EdwinJaraOFC/VentusSolarisAnalyzer/Documentacion/Talleres/Taller 04/T04Modelado3D.md

<p align="left">
  
  <h1 align="center">Taller 04: Modelado 3D</h1>
</p>

## 1. Descripción del Modelado 3D (Onshape)

### Características y componentes de Onshape

<p align="justify">
  
- **Modelado paramétrico:** Permite realizar cambios en el diseño de forma rápida y eficiente.<br>
- **Colaboración en tiempo real:** Los usuarios pueden trabajar en un mismo diseño de forma simultánea.<br>
- **Acceso basado en la nube:** Al estar basado en la nube, Onshape permite a los usuarios acceder a sus diseños desde cualquier dispositivo con conexión a internet.<br>
- **Versionado automático:** Onshape guarda automáticamente el historial de versiones de los diseños
</p>

### Importancia del Onshape como herramienta para la creación del modelado 3D

<p align="justify">
Onshape es una herramienta importante para el modelado 3D debido a su accesibilidad, capacidad de colaboración, modelado paramétrico y herramientas integradas para simulaciones y pruebas de rendimiento. Estas características hacen de Onshape una plataforma integral y poderosa para el diseño y la ingeniería colaborativa en 3D.
</p>

## 2. Materiales
- Laptop e implementos
- Software CAD (Onshape)
- Impresora 3D

## 3. Desarrollo de ejercicios
### Ejercicio 1: Representación de un vaso a partir de un círculo

<p align="justify">
Para realizar la representación de un vaso 3D, nos ubicamos en la vista “Top” para añadir un círculo con dimensiones de 60mm, luego nos encargamos de que el círculo se encuentre centrado con la opción “Concentric”.
</p>

<div align="center"; style="display: flex; justify-content: space-between;">
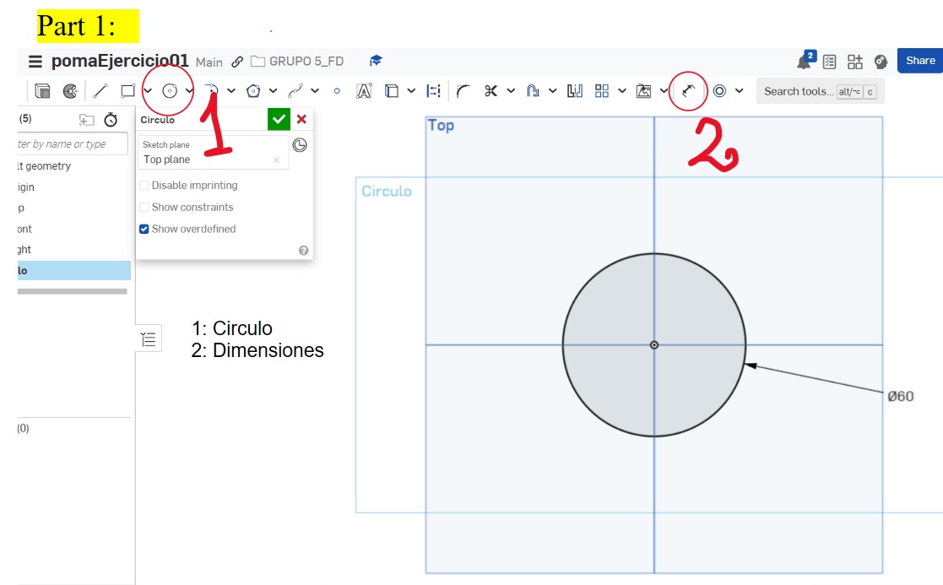
[picture p34: Documentacion/Talleres/Taller 04/Imagenes/T04Imagen01.jpg]
  
</div>

<p align="justify">
Luego realizamos las accion “Extrude” para pasar de un modelo 2D a un modelo 3D con ciertas medidas.
</p>

<div align="center"; style="display: flex; justify-content: space-between;">
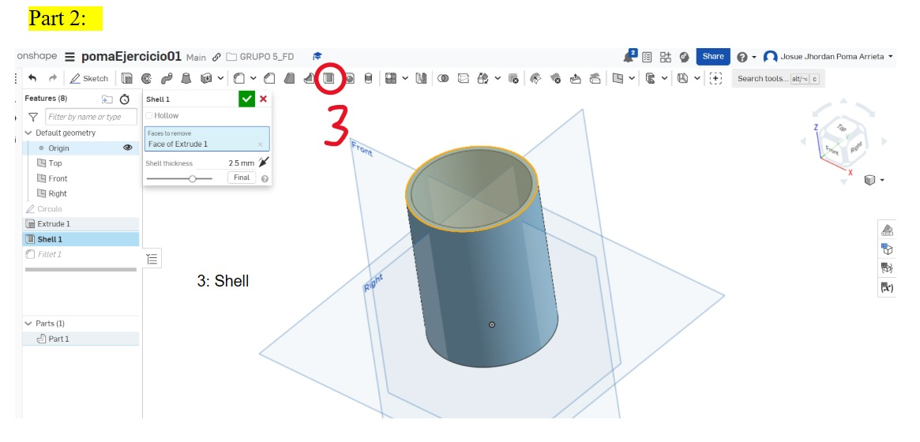
[picture p35: Documentacion/Talleres/Taller 04/Imagenes/T04Imagen02.jpg]
  
</div>

<p align="justify">
Después pasamos a quitarle la parte superior del vaso para que se parezca cada vez más un vaso, con la opción de “Shell”.
</p>

<div align="center"; style="display: flex; justify-content: space-between;">
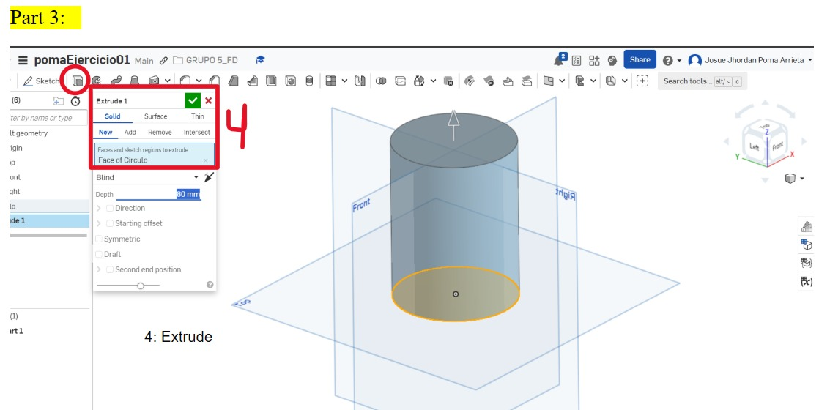
[picture p36: Documentacion/Talleres/Taller 04/Imagenes/T04Imagen03.jpg]
  
</div>

<p align="justify">
Le dimos bordes con la opción “Fillet”, quedando nuestro vaso de la siguiente manera:
</p>

<div align="center"; style="display: flex; justify-content: space-between;">
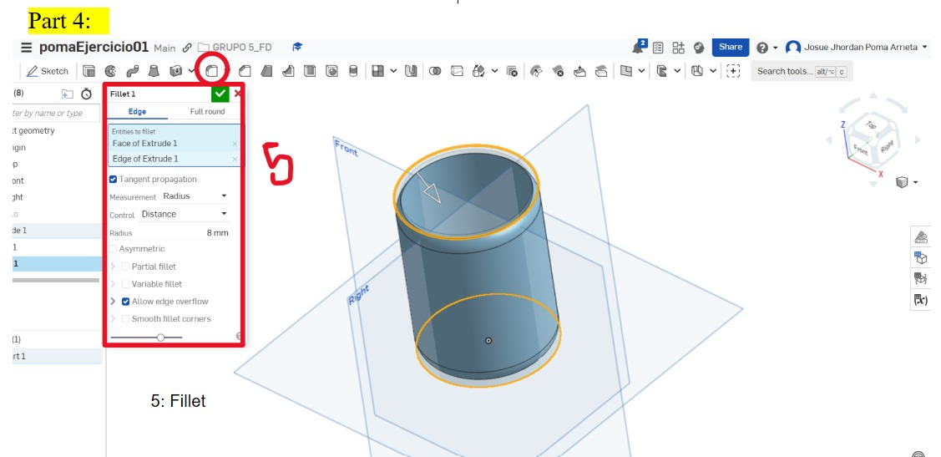
[picture p37: Documentacion/Talleres/Taller 04/Imagenes/T04Imagen04.jpg]
  
</div>

<p align="justify">
Después escogimos que color queríamos para el vaso y lo seleccionamos.
</p>

<div align="center"; style="display: flex; justify-content: space-between;">
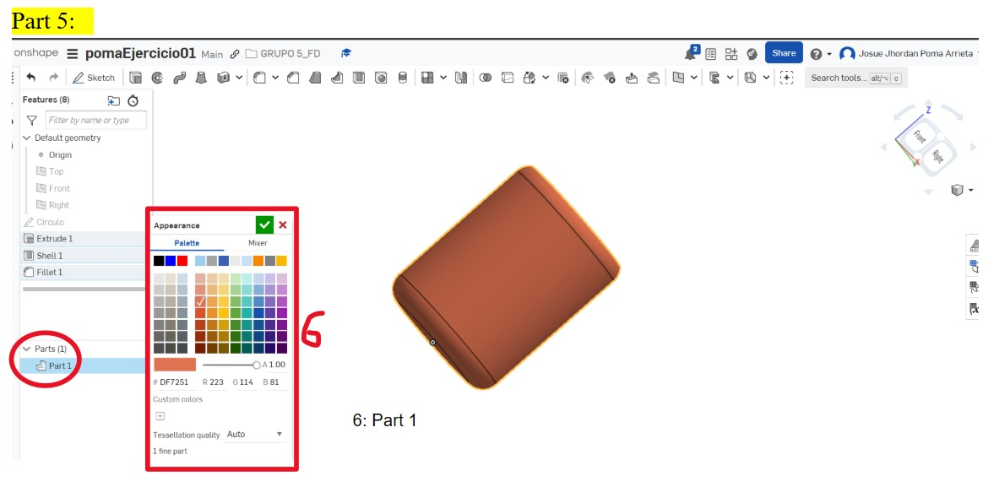
[picture p38: Documentacion/Talleres/Taller 04/Imagenes/T04Imagen05.jpg]
  
</div>

<p align="justify">
Finalmente quedando nuestro diseño del vaso de la siguiente manera:
</p>

<div align="center"; style="display: flex; justify-content: space-between;">
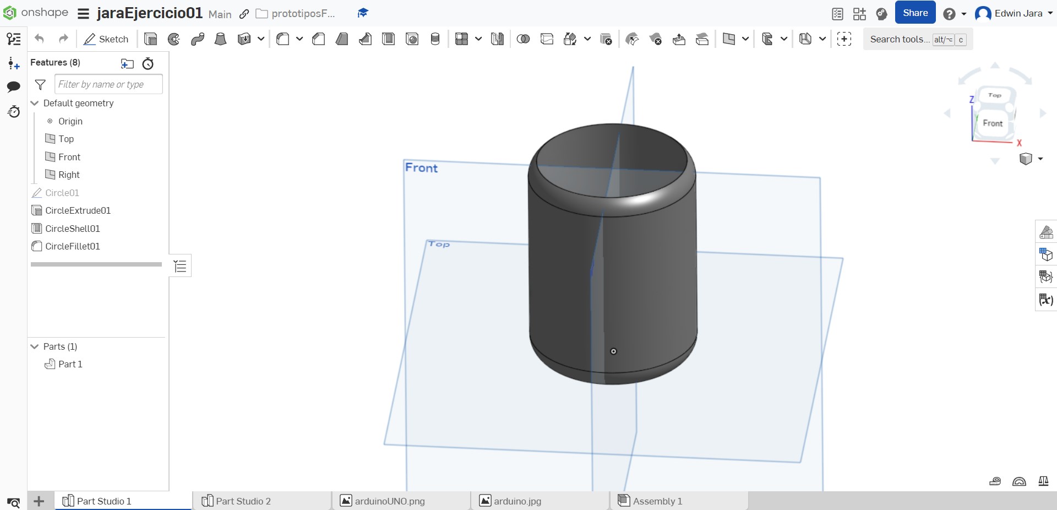
[picture p39: Documentacion/Talleres/Taller 04/Imagenes/T04Imagen06.jpg]
  
</div>

### Ejercicio 2: Representación de un vaso a partir de líneas

Para realizar la representación de un vaso 3D a partir de líneas, comenzamos en la vista "front" y creamos un sketch donde agregamos líneas para esbozar la mitad del vaso en 2D. Utilizando funciones aprendidas en el ejercicio 1, transformamos este diseño bidimensional en uno tridimensional. Las herramientas empleadas permitieron extruir y dar forma al vaso 2D, generando así la representación final en 3D, como se muestra en la segunda imagen.

<div align="center"; style="display: flex; justify-content: space-between;">
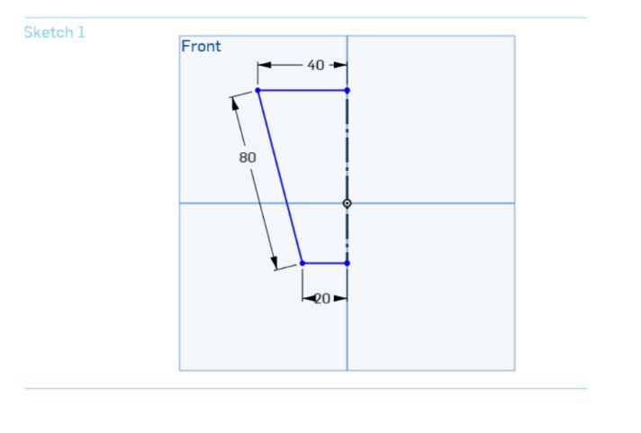
[picture p40: Documentacion/Talleres/Taller 04/Imagenes/T04Imagen07.jpg]
  
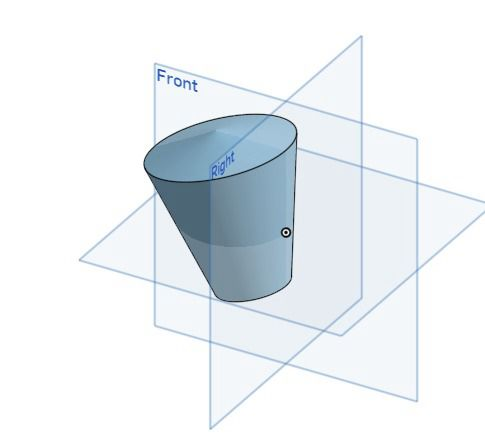
[picture p41: Documentacion/Talleres/Taller 04/Imagenes/T04Imagen08.jpg]
  
</div>

### Ejercicio 3: Representación de una taza a partir del ejercicio 1

<p align="justify">
Para modelar la taza tuvimos que usar el molde ya hecho de un vaso en el ejercicio 1, partimos ese molde y lo transformamos en una taza funcional y estéticamente diferente al añadirle una asa. Comenzamos dibujando la asa con la herramienta "3 point arc" en un nuevo sketch, ajustándola cuidadosamente para que se integrara bien con la forma existente del vaso. Luego, utilizando las herramientas de modelado en 3D, dimos volumen y forma ergonómica a la asa, haciendo ajustes hasta lograr un diseño atractivo. Finalmente, refinamos la transición entre la asa y el cuerpo del vaso para obtener una apariencia suave y cohesiva.
</p>

<div align="center"; style="display: flex; justify-content: space-between;">
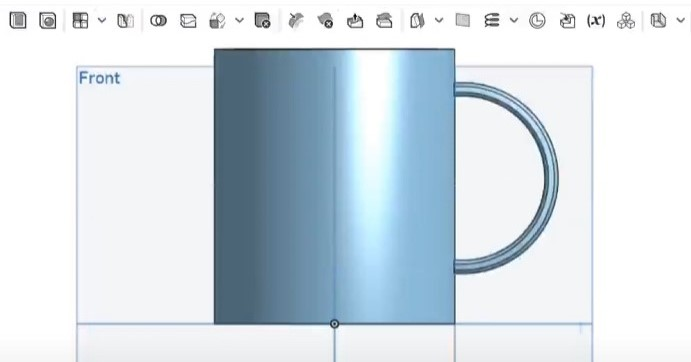
[picture p42: Documentacion/Talleres/Taller 04/Imagenes/T04Imagen22.jpg]
  
</div>

### Ejercicio 4: Representación de un case para Arduino UNO

<p align="justify">
Para realizar la representación del case Arduino UNO, empezamos insertando una imagen en un sketch en “top” y redimensionando un poco para posteriormente empezar a hacer el case.
</p>

<div align="center"; style="display: flex; justify-content: space-between;">
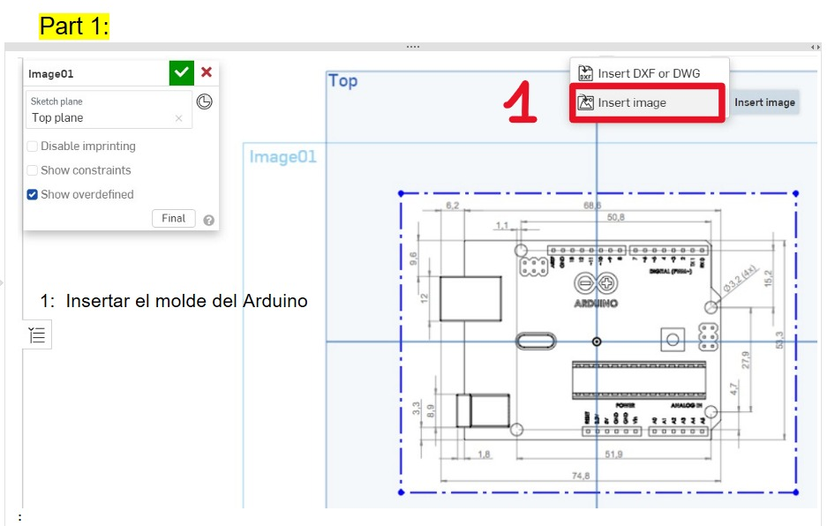
[picture p43: Documentacion/Talleres/Taller 04/Imagenes/T04Imagen13.jpg]
  
</div>

<p align="justify">
Luego de insertar la imagen procedemos a crear un sketch en “top” e insertar líneas tomando la forma del case, luego procedemos a insertar las dimensiones correspondientes.
</p>

<div align="center"; style="display: flex; justify-content: space-between;">
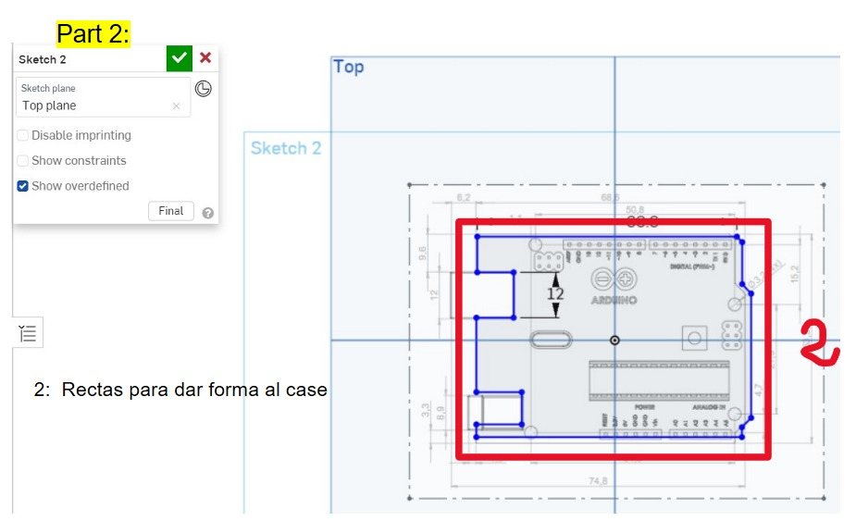
[picture p44: Documentacion/Talleres/Taller 04/Imagenes/T04Imagen14.jpg]
  
</div>

<p align="justify">
Luego usamos la función “extrude” con las líneas hechas anteriormente para darle la forma 3D a nuestro trabajo.
</p>

<div align="center"; style="display: flex; justify-content: space-between;">
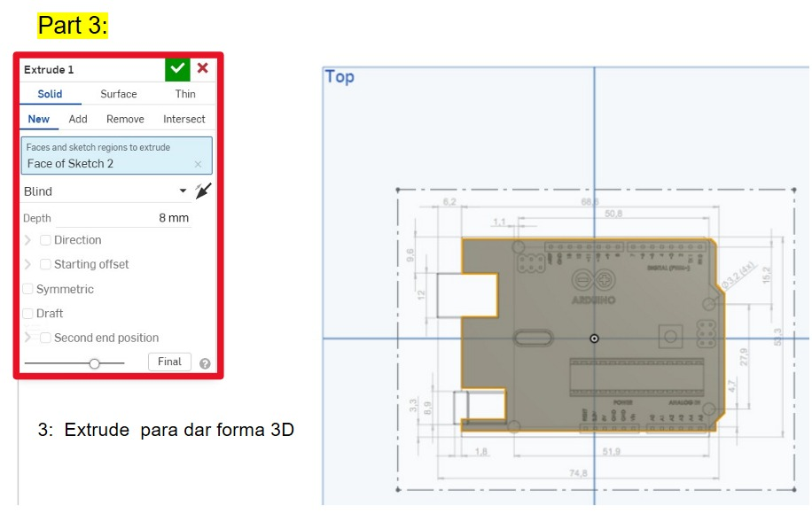
[picture p45: Documentacion/Talleres/Taller 04/Imagenes/T04Imagen15.jpg]
  
</div>

<p align="justify">
Luego decidimos quitarle la tapa para que se asemeje al case del Arduino UNO, junto con asignarle un grosor que fue de 1mm.
</p>

<div align="center"; style="display: flex; justify-content: space-between;">
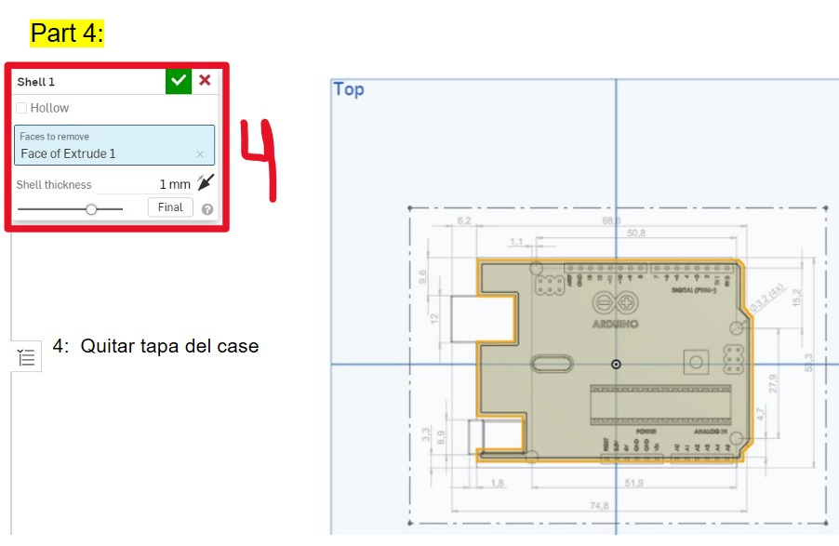
[picture p46: Documentacion/Talleres/Taller 04/Imagenes/T04Imagen16.jpg]
  
</div>

<p align="justify">
Paso extra: Tuvimos que recortar las partes que hacían que el case no entre correctamente luego de darnos cuenta en la impresión 3D, lo hicimos creando un sketch nuevo y dando la forma del rectángulo.
</p>

<div align="center"; style="display: flex; justify-content: space-between;">
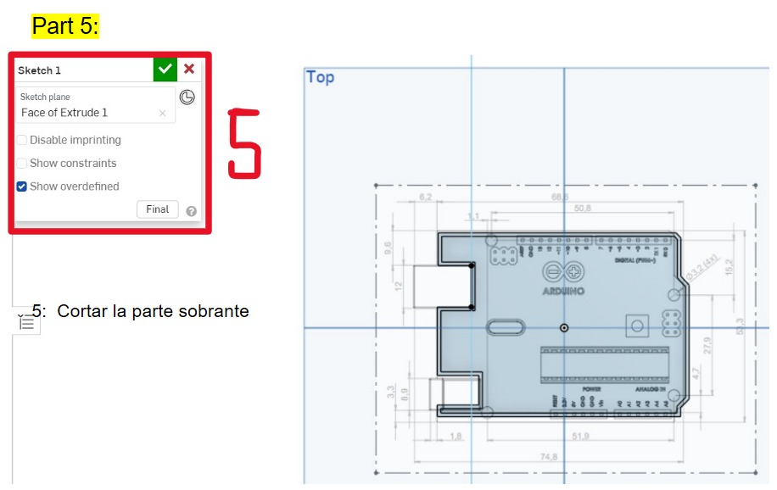
[picture p47: Documentacion/Talleres/Taller 04/Imagenes/T04Imagen17.jpg]
  
</div>

<p align="justify">
Paso extra: Usamos la función "extrude" pero con la diferencia de que esta vez la usamos parar borrar la parte que no necesitabamos del case, usando anteriormente los rectángulos, luego ajustamos y damos en enter para completar la eliminación de ese espacio.
</p>

<div align="center"; style="display: flex; justify-content: space-between;">
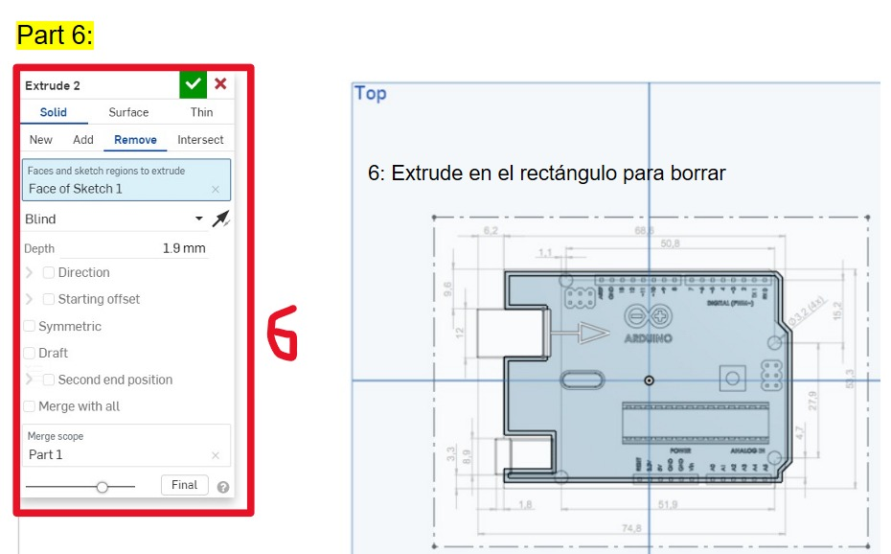
[picture p48: Documentacion/Talleres/Taller 04/Imagenes/T04Imagen18.jpg]
  
</div>

<p align="justify">
Y al final de todos estos pasos el modelado del case Arduino UNO nos quedó de la siguiente manera:
</p>

<div align="center"; style="display: flex; justify-content: space-between;">
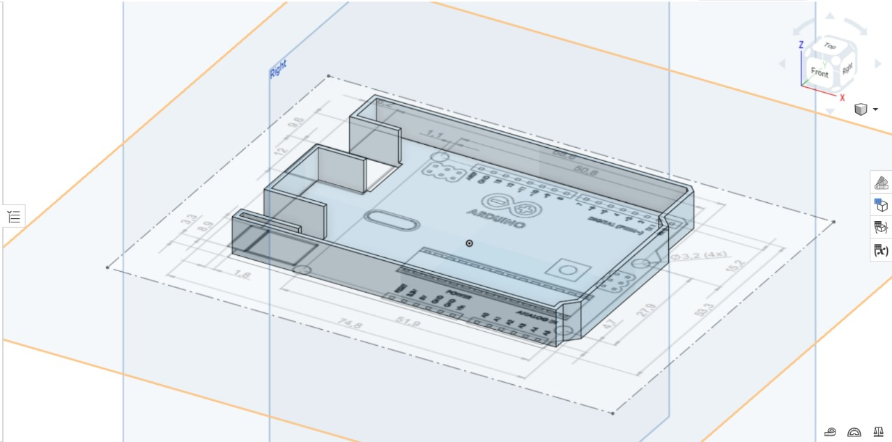
[picture p49: Documentacion/Talleres/Taller 04/Imagenes/T04Imagen19.jpg]
  
</div>

<br>
<p align="justify">
Al momento de imprimir nuestro modelado 3D no tomamos en cuenta que el case debía tener un grosor mínimo de 5mm, nosotros lo hicimos con un grosor de 1mm, por lo que nuestro case salió delgado, y tuvimos otro pequeño error de no considerar los espacios de las entradas del Arduino. Anotamos estos errores para no volverlos a cometer en un futuro.
</p>

<div align="center"; style="display: flex; justify-content: space-between;">
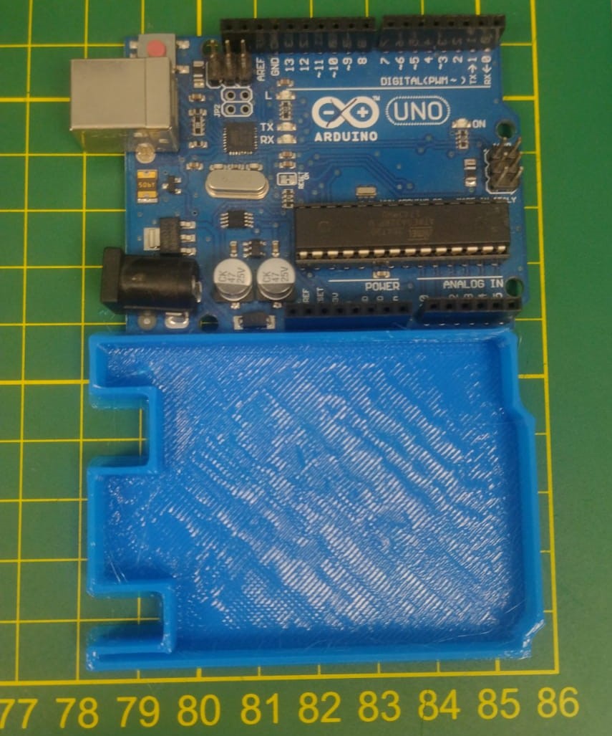
[picture p50: Documentacion/Talleres/Taller 04/Imagenes/T04Imagen20.jpg]
  
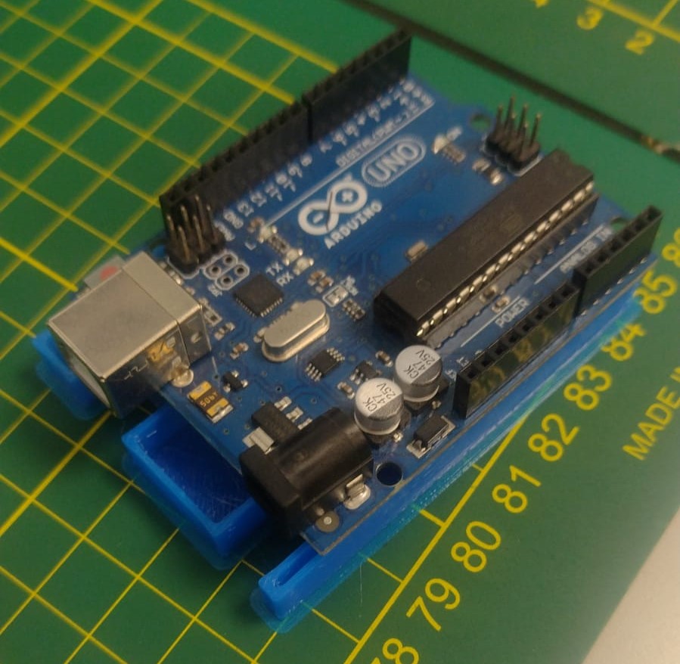
[picture p51: Documentacion/Talleres/Taller 04/Imagenes/T04Imagen21.jpg]
  
</div>

## 4. Evidencias del desarrollo de ejercicios

<div align="center"; style="display: flex; justify-content: space-between;">
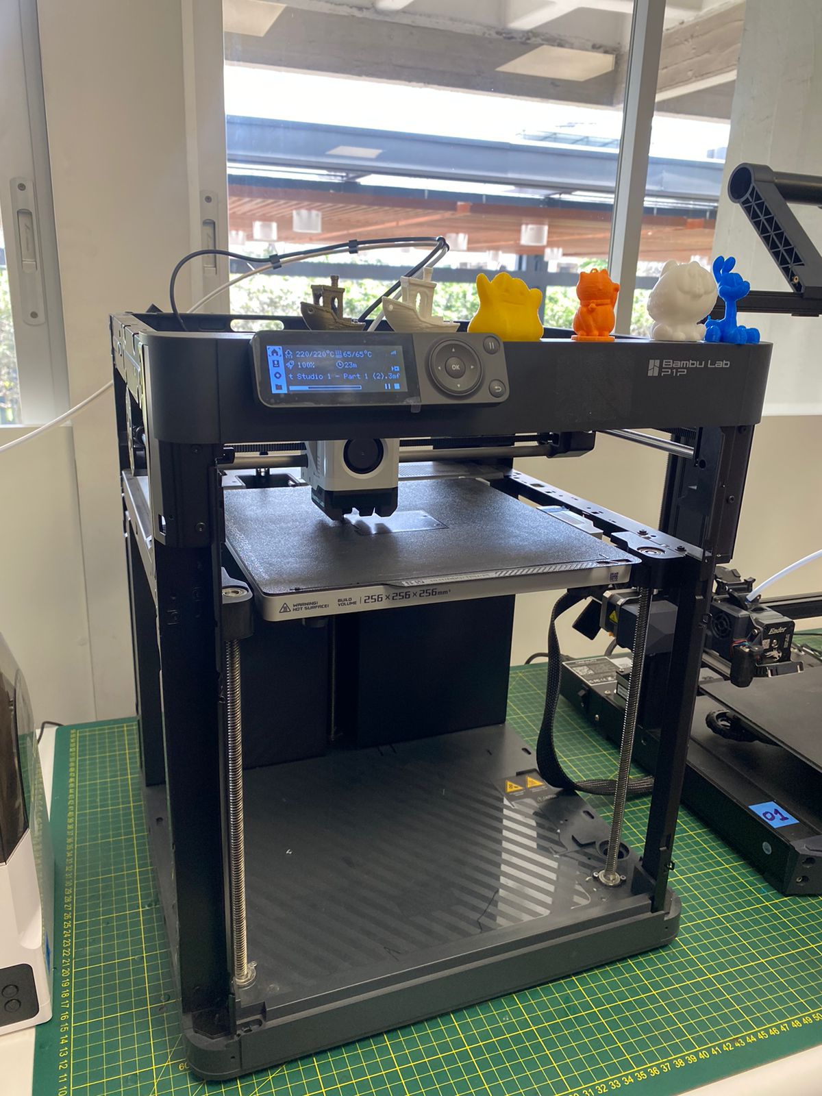
[picture p52: Documentacion/Talleres/Taller 04/Imagenes/T04Imagen09.jpg]
  
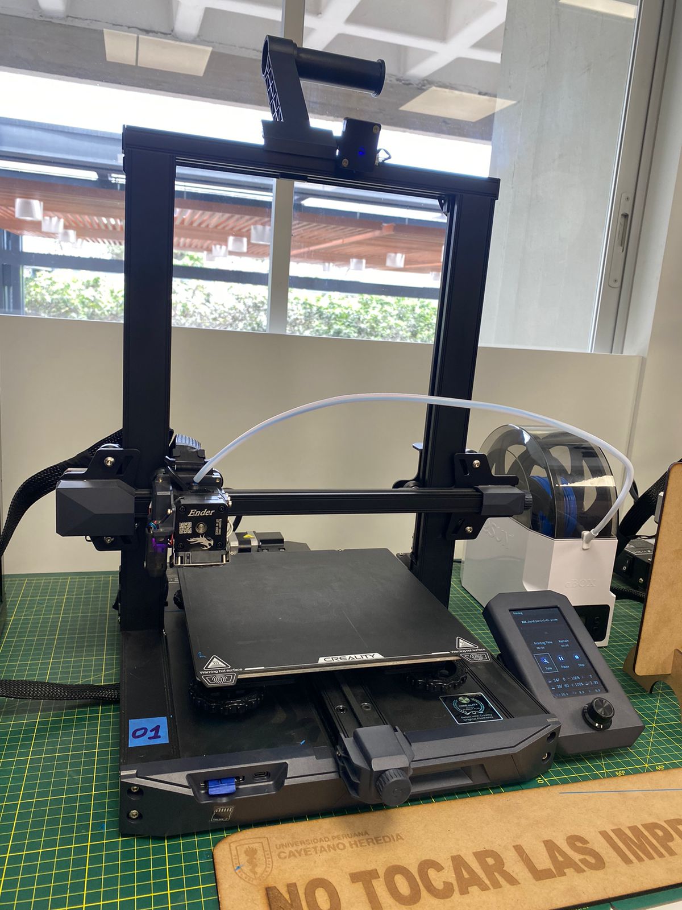
[picture p53: Documentacion/Talleres/Taller 04/Imagenes/T04Imagen10.jpg]
  
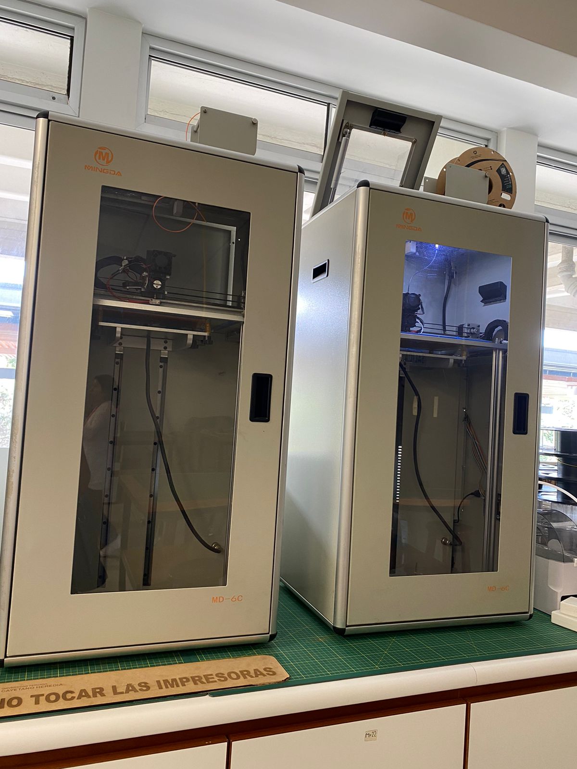
[picture p54: Documentacion/Talleres/Taller 04/Imagenes/T04Imagen11.jpg]
  
</div> 
</div>
<div align="center"; style="display: flex; justify-content: space-between;">
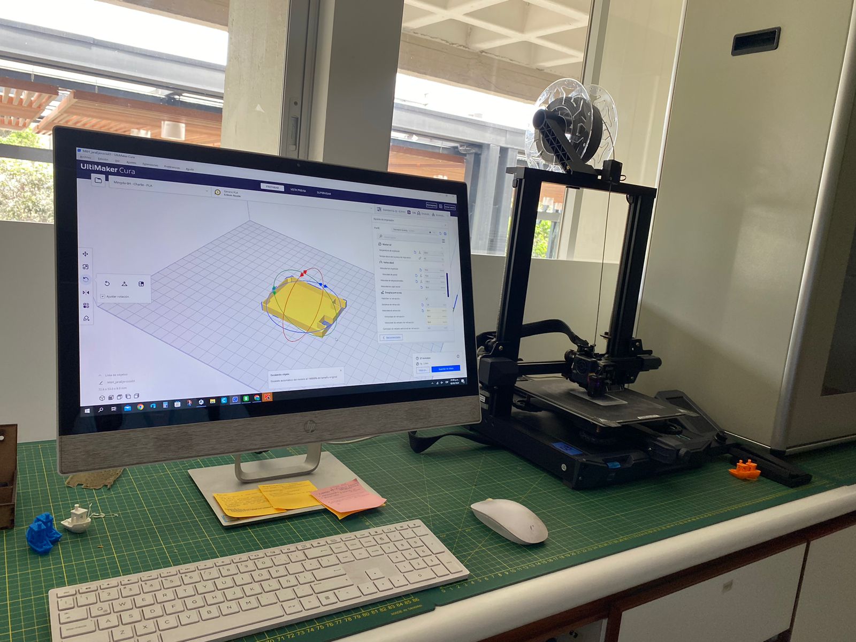
[picture p55: Documentacion/Talleres/Taller 04/Imagenes/T04Imagen12.jpg]
  
</div>

## 5. Conclusión

<p align="justify">
Durante la sesión de clase en la que modelamos una vaso ,  taza en la aplicación de Onshape y posteriormente creamos un estuche para un Arduino, adquirimos conocimientos prácticos sobre el modelado en 3D y la aplicación de Onshape. Esta experiencia nos permitió aplicar las habilidades aprendidas en un entorno práctico y nos preparó para el proceso de impresión 3D. En resumen, esta actividad fue fundamental para el desarrollo de nuestras habilidades en el campo del diseño y la fabricación digital.
</p>
