EdwinJaraOFC/VentusSolarisAnalyzer/Documentacion/Presentaciones/Proyectos de Ingenieria/Hito01.pdf

# INTEGRANTES:

# Florian Párraga, Josué Abel Jara Bocanegra, Edwin Junior Pérez Amado, Romina Alisson Pérez Damián, Cindy Mayomi

Vásquez Nuñez America Mailyn | GRUPO N°6

# "Ventus Solaris"

# Deseos:

"Sistema portátil de baja potencia a base de
sensores | que | puedan | monitorear | las características de la radiación solar y la

velocidad del viento, con el objetivo de transmitir datos desde los sensores y dispositivos IoT a una

plataforma en la nube de gestión centralizada".

Problematica: Falta de acceso a la electricidad

en el colegio San José Obrera 15357, específicamente en el km 41 carretera a Chulucanas.

Autoridades locales interesadas en mejorar el acceso a la energía en la zona rural, con el objetivo de garantizar que las actividades educativas del colegio San José Obrero no se

vean interrumpidas por cortes prolongados de electricidad.

## Solución:

## Lugar de estudio:

I.E. San Jose Obrero - Morropón, Chulucanas - Piura

## REQUERIMIENTOS PARA EL USUARIO:

Necesidades: Acceso Continuo a la Electricidad Costo Accesible Fiabilidad para la Educación Facilidad de Mantenimiento

Deseos: Capacitación del personal Mejora de la Infraestructura Educativa

Impacto en la Comunidad Durabilidad a Largo Plazo

# Requerimientos del Sistema:

# Necesidades:

Fácil Configuración y Operación Medición | Precisa | de | Variables Climáticas Autonomía Energética Bajo Costo de Producción Portabilidad
Optimización del Consumo de Energía Capacidad de Almacenamiento

Local Resiliencia Climática Conectividad para Transmisión de Datos

## Usuarios (stakeholders):

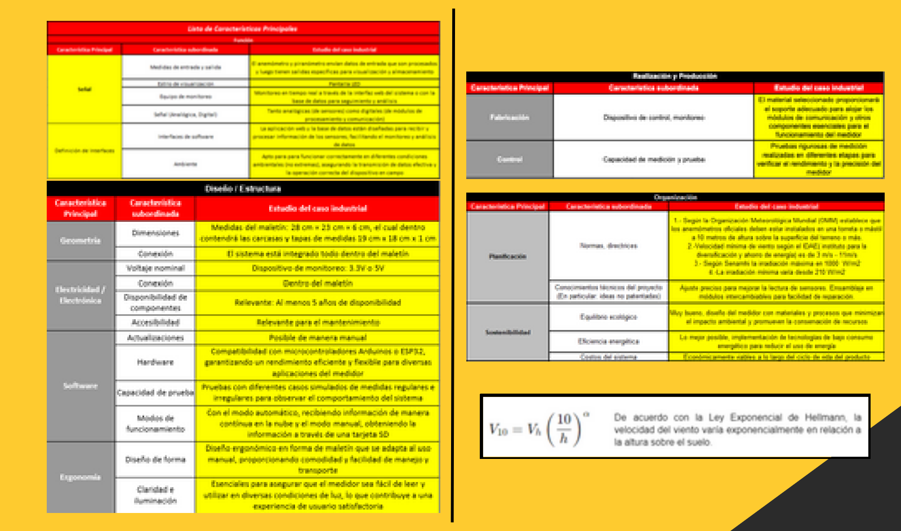
[picture p56: page 3]
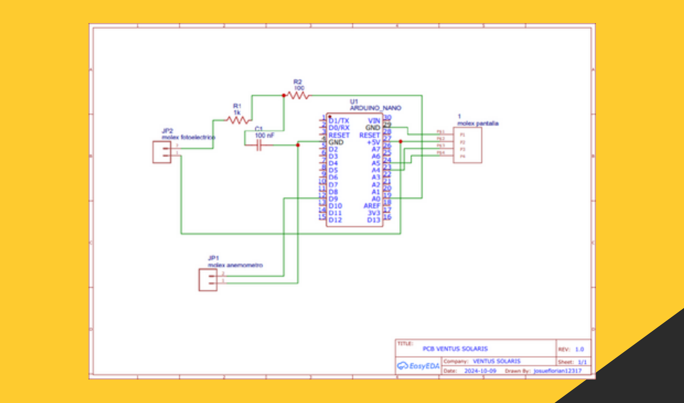
[picture p57: page 4]

# PCB DEL CIRCUITO ELECTRÓNICO

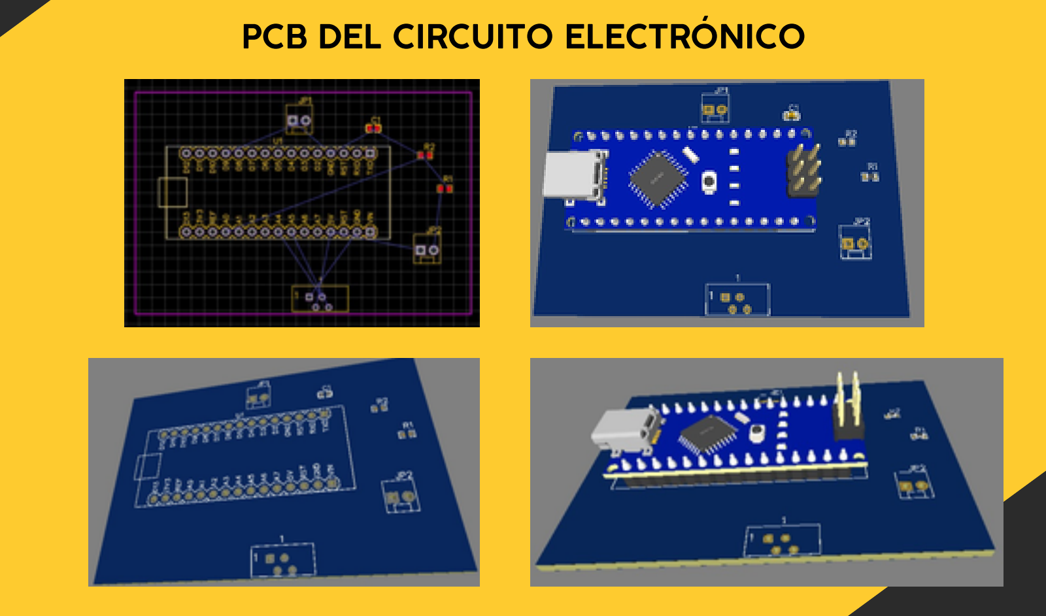
[picture p58: page 5]

# COMPONENTES PRINCIPALES

PCB DEL CIRCUITO ELECTRÓNICO.

Objetivo del Proyecto: Desarrollar un sistema portátil de baja potencia que monitoriza: Radiación solar (Sensor SUF268J001). Velocidad del viento (Anemómetro casero con motor RF-500TB-14415).

Arduino Nano
(Microcontrolador)

Sensor de Radiación Solar (SUF268J001)

Anemómetro Casero

Pantalla I2C

Conectores Molex

Facilitan | conexiones modulares de sensores y pantalla, asegurando fácil mantenimiento

Muestra datos en tiempo real (radiación solar y velocidad del viento). Comunicación vía pines A4

(SDA) y A5 (SCL).

Calcula la velocidad del viento en función de las revoluciones del motor. Envía la señal al pin ADC (A1) del Arduino.

Mide la intensidad de la
radiación solar. Envía datos al pin ADC

(A0) del Arduino Nano.

Controla los sensores y la pantalla I2C. Alimenta los componentes a

través de sus pines de 5V.

# VENTAJAS:

Modularidad: Uso de conectores Molex para rápida desconexión y ajuste de componentes. Eficiencia Energética: Optimizado

para bajo consumo con alimentación de batería portátil. Portabilidad: Diseño compacto para

fácil instalación en campo.

Conclusión: El sistema portátil para medir la velocidad del viento y la radiación solar está diseñado

para proporcionar datos precisos y en tiempo real, facilitando la evaluación de proyectos de energía renovable. El uso de conectores Molex y un diseño optimizado

garantiza la modularidad, eficiencia y facilidad de uso del sistema en campo.

# COMPONENTES

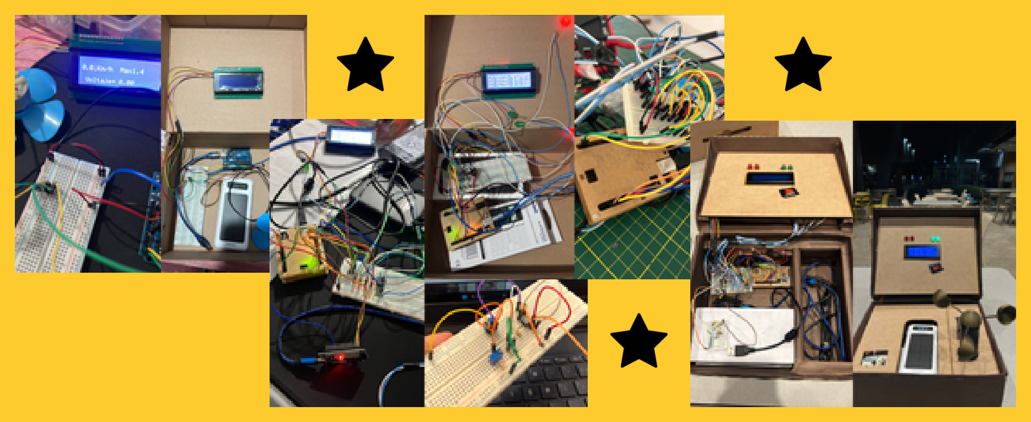
[picture p59: figure]

Álvarez, C. (2006, September). Energía eólica (IDAE, Ed.) [Review of Energía eólica]. Instituto Para La Diversificación Y Ahorro de La Energía; | Instituto | para | la | Diversificación | y | Ahorro | de | la | Energía. http://www.esengrupo.com/uploads/descargas/archivo/Manual%20de%20Energ%C3%ADa%20E%C3%B3lica%20IDAE.pdf

Fap Wilar, M., Molina, G., Fap, C., Cruzado, R., Senamhi, D., & Quijandría Salmón, J. (n.d.). SERVICIO NACIONAL DE METEOROLOGÍA E HIDROLOGÍA DIRECCIÓN GENERAL DE INVESTIGACIÓN Y ASUNTOS AMBIENTALES MINISTERIO DE

ENERGÍA Y MINAS DIRECCIÓN EJECUTIVA DE PROYECTOS REPÚBLICA DEL PERÚ ATLAS DE ENERGÍA SOLAR DEL PERÚ. https://www.senamhi.gob.pe/pdf/Atlas%20_de_Radiacion_Solar.pdf

Ruíz de Alegría, A. (2020). Estudio complementario de impacto de la radiación UV en paneles solares (datos UV de un año) y otros componentes expuestos en condiciones del altiplano boliviano (Dirección General de Energías AlternativaS, Ed.) [Review of Estudio complementario de impacto de la radiación UV en paneles solares (datos UV de un año) y otros componentes expuestos en condiciones del altiplano boliviano]. Electricidad Y Energías Alternativas; Programa de Energías Renovables (PEERR). https://energypedia.info/images/3/31/APRBADO_INFORME_estudio_UV.pdf

Uribe, I. M. (2018). Valoración del viento como fuente de energía eólica en el estado de Guerrero. Ingeniería, 22(3), 30-46. https://www.redalyc.org/journal/467/46759491003/46759491003.pdf

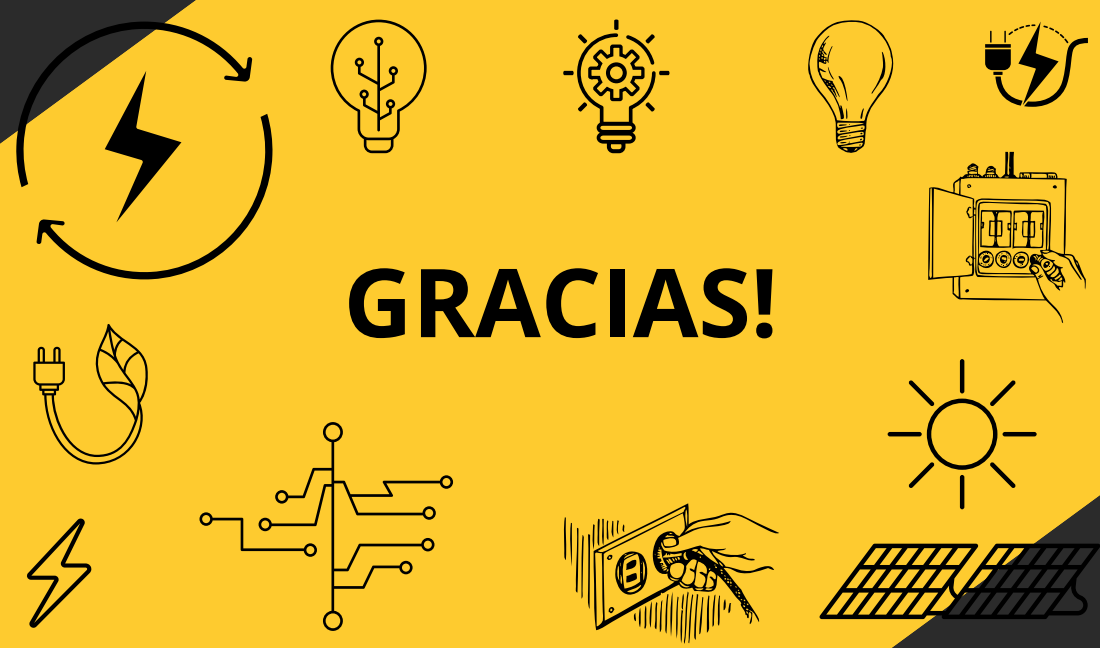
[picture p60: page 9]
GRACIAS!
