EdwinJaraOFC/VentusSolarisAnalyzer/Prototipo/README.md

<p align="left">
  
  <h1 align="center">Desarrollo de Prototipo</h1>
</p>

<p align="justify">La carpeta Prototipo contiene todos los recursos necesarios para la creación, implementación y pruebas del prototipo del proyecto VentusSolaris Analyzer. Aquí se encuentra la documentación y los archivos que respaldan el desarrollo técnico del hardware y software, así como los resultados de las pruebas realizadas.</p>

## Estructura de la Carpeta

### 1. Diseño

- Esquemas y planos del prototipo.
- Documentos relacionados con el diseño conceptual y técnico.
- Diagramas y modelos 3D, si están disponibles.

### 2. Hardware

- Especificaciones de los componentes electrónicos y mecánicos utilizados.
- Esquemas de conexión y diagramas de circuitos.
- Manuales de instalación y configuración del hardware.

### 3. Software

- Código fuente del proyecto.
- Scripts y programas necesarios para la operación del prototipo.
- Documentación sobre las dependencias y configuraciones del software.

### 4. Tests

- Resultados de las pruebas realizadas al prototipo.
- Métodos de validación para hardware y software.
- Registros de errores y mejoras propuestas.

## Propósito

<p align="justify">La carpeta Prototipo está diseñada para ofrecer una visión integral del proceso de desarrollo técnico, desde el diseño inicial hasta las pruebas finales. Su contenido está orientado a:</p>

1. Facilitar la replicación del prototipo por otros equipos interesados en el proyecto.
2. Documentar los avances y resultados obtenidos durante las etapas de desarrollo.
3. Optimizar el diseño a través de pruebas continuas y retroalimentación.

## Uso

1. Explora la carpeta Diseño para comprender la planificación inicial del prototipo.
2. Revisa el apartado Hardware para ensamblar y configurar los componentes físicos.
3. Consulta la sección Software para implementar y ejecutar el código del proyecto.
4. Verifica la carpeta Tests para analizar los resultados y evaluar el desempeño del sistema.

## Contribuciones

<p align="justify">Si deseas colaborar en la mejora del prototipo, consulta los documentos dentro de las carpetas Diseño y Tests para identificar áreas de mejora y proponer cambios. Asegúrate de seguir las guías de contribución detalladas en el README general.</p>
