EdwinJaraOFC/VentusSolarisAnalyzer/Prototipo/Diseño/README.md

<p align="left">
  
  <h1 align="center">Diseño del Prototipo</h1>
</p>

<p align="justify">Esta carpeta contiene los recursos y documentos relacionados con el diseño estructural y conceptual del proyecto VentusSolaris Analyzer. Incluye desde los modelos iniciales hasta el diseño final del prototipo.</p>

## Contenido

- <strong>D01ModeladoBase:</strong> Documentación del modelado inicial, incluyendo conceptos preliminares y bocetos.

- <strong>D02PlanosBase:</strong> Planos técnicos que detallan las dimensiones y estructuras del prototipo.

- <strong>D03DiseñoFinal:</strong> Representación del diseño final aprobado para la fabricación y ensamblaje.

## Uso

- Revisa el modelado base para comprender las ideas iniciales del diseño.
- Consulta los planos base para obtener especificaciones técnicas del prototipo.
- Explora el diseño final como referencia para la implementación y mejoras futuras.
