EdwinJaraOFC/VentusSolarisAnalyzer/Documentacion/Investigacion/README.md

<p align="left">
  
  <h1 align="center">Investigación</h1>
</p>

<p align="justify">Esta carpeta contiene los documentos esenciales relacionados con la etapa de investigación del proyecto VentusSolaris Analyzer. En estos archivos se detallan los análisis, estudios y enfoques que sustentan el diseño y desarrollo del prototipo.</p>

## Contenido

- <strong>I01DefiniciónDelProblema:</strong> Planteamiento y delimitación del problema abordado por el proyecto.

- <strong>I02ContextoSocialEconomico:</strong> Análisis del impacto social y económico del proyecto en diversas comunidades.

- <strong>I03EstadoDelArte:</strong> Investigación de tecnologías y enfoques existentes en el ámbito de las energías renovables.

- <strong>I04CajaNegraEsquemaDeFunciones:</strong> Diagramas y descripción funcional del sistema desarrollado.

- <strong>I05MatrizMorfológicaTablaValoración:</strong> Evaluación de alternativas de diseño mediante herramientas morfológicas.

- <strong>I06ListaDeCaracterísticas&RequerimientosPrincipales:</strong> Resumen de las especificaciones y requisitos clave del sistema.

## Uso

<p align="justify">Revisa los documentos en el orden numerado para comprender el flujo lógico de la investigación, desde la definición del problema hasta los requerimientos principales que dieron forma al proyecto.</p>
