EdwinJaraOFC/VentusSolarisAnalyzer/Documentacion/Presentaciones/Fundamentos de Diseño/Hito02.md

<p align="left">
  
  <h1 align="center">Hito 02</h1>
</p>

## Poster para Presentación Final

<p align="center">
  
</p>

## Fotografía del Proyecto Final

<p align="center">
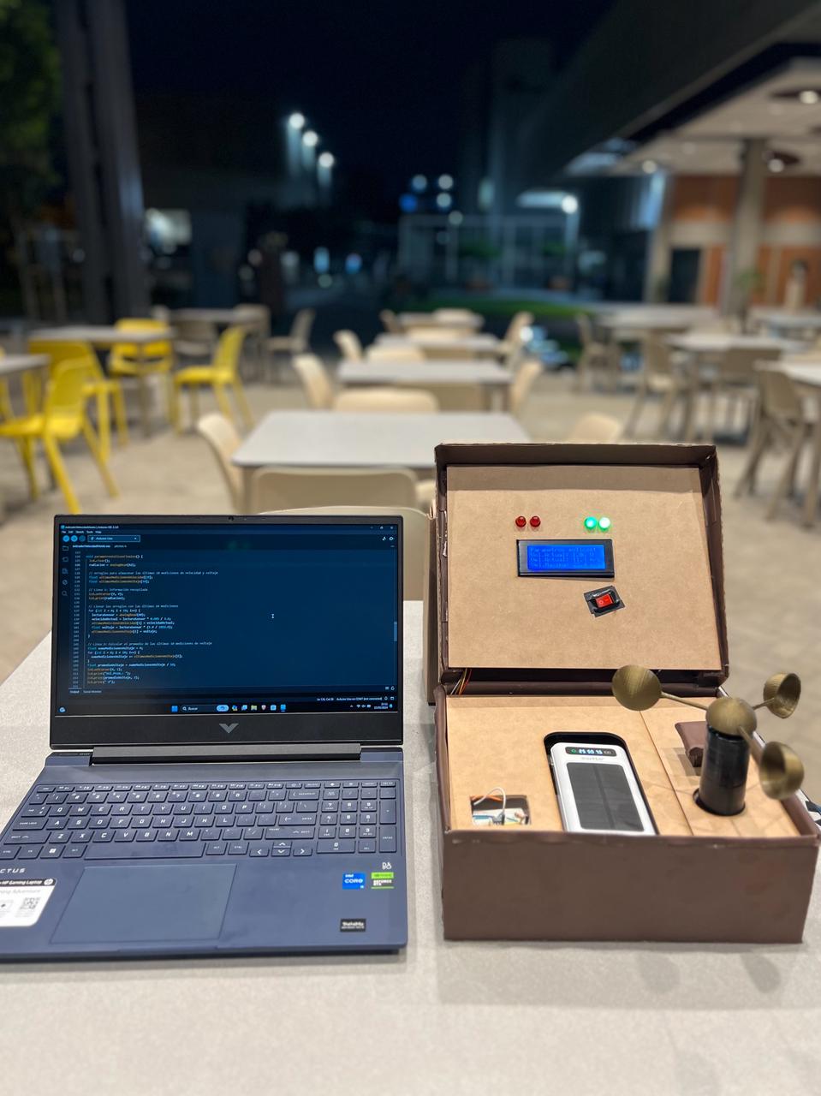
[picture p61: Documentacion/Presentaciones/Fundamentos de Diseño/Imagenes/H02Imagen02.jpg]
  
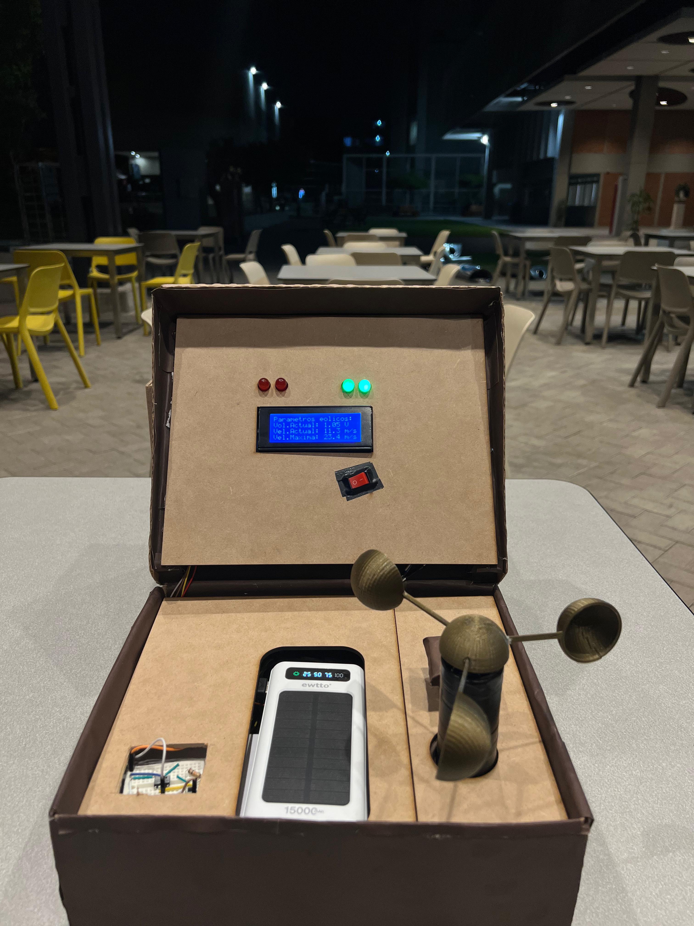
[picture p62: Documentacion/Presentaciones/Fundamentos de Diseño/Imagenes/H02Imagen03.jpg]
  
</p>
