EdwinJaraOFC/VentusSolarisAnalyzer/Documentacion/Investigacion/I02ContextoSocialEconomico.md

<p align="left">
  
  <h1 align="center">Contexto Social y Económico</h1>
</p>

# Impactos Sociales de la Falta de Suministro Eléctrico en Piura, Perú

## 1. **A Nivel Regional**

<p align="justify">
En Perú, más de 700 mil hogares carecen de conexión al Sistema Eléctrico Interconectado Nacional, siendo alrededor de 21 mil viviendas rurales en Piura las afectadas, según datos del Instituto Nacional de Estadística e Informática (INEI). Estos indican que aproximadamente el 5% de las viviendas en la región no tienen acceso al alumbrado eléctrico de la red pública, y un 11% de la población depende de la biomasa como fuente de energía, recolectando leña y enfrentando diversos obstáculos.

La situación de pobreza energética evidencia la falta de desarrollo sostenible. En este entorno, el Banco Interamericano de Desarrollo (BID) destaca que el acceso a servicios básicos como iluminación, cocción y refrigeración no solo afecta a los hogares, sino que también incide en la pobreza de tiempo de las mujeres, limitando sus oportunidades para realizar otras actividades significativas en su día, como estudiar, recrearse o generar ingresos a través de emprendimientos o el trabajo en el mercado laboral (Amaya, 2023).
</p>

<p align="center">
  
</p>

## 2. **A Nivel Nacional**

<p align="justify">
El informe destaca una persistente brecha de acceso al servicio eléctrico entre zonas rurales y urbanas, aunque ha disminuido relativamente en el último año. Mientras la mayoría de los departamentos costeros supera el  aproximandamente el 97% de acceso, Loreto y Amazonas presentan niveles inferiores al 88%.

Según la Encuesta Nacional de Hogares del INEI, el suministro eléctrico no está disponible en el 42% de las áreas rústicas de la selva. En contraste, las áreas  rurales como la costa y sierra tienden al acceso de 78.5% y 72.4%, respectivamente. Estas disparidades resaltan la necesidad urgente de estrategias específicas para abordar los desafíos únicos de cada área y garantizar la equidad en el acceso a la electricidad a nivel nacional (Osinergmin, 2019-2020).
</p>

<p align="center">
  
</p>

## **3. A Nivel Mundial**

<p align="justify">
La limitación en la disponibilidad eléctrica a nivel mundial constituye un desafío de considerable magnitud para el avance y la prosperidad de las comunidades, especialmente en países subdesarrollados. Esta carencia repercute en diversos aspectos sociales, económicos y ambientales, generando consecuencias graves y multifacéticas.

De acuerdo con Paul Akiwumi, representante de la UNCTAD, la ausencia de la energía conlleva serias repercusiones en el avance del sector industrial dentro de las naciones en vías de desarrollo. Aproximadamente, el 1.8% de asistencia se asigna al ámbito energético, a pesar de su papel fundamental en el progreso (Moran, M., 2017).

Asegurar el acceso energético universal se presenta como una necesidad imperativa para reducir la brecha en el desarrollo global y mejorar las condiciones en una gran parte de la población. La implementación de soluciones sostenibles se erige como un pilar fundamental para alcanzar este objetivo, abordando los desafíos desde una perspectiva integral que considere factores sociales, económicos y ambientales.
</p>

<div align="center"; style="display: flex; justify-content: space-between;">
  
  
</div>

# Impacto Económico de la Privación de Suministro a la Energía Eléctrica en Piura, Perú

## **1. A Nivel Regional**

En la región de Piura, se ha evidenciado una producción considerable de gigavatios de energía eléctrica, según la tabla del informe del Ministerio de Energía y Minas para el año 2021. Es relevante señalar que la generación térmica destaca como la más notable en términos de cantidad. Sin embargo, esta predominancia podría tener implicaciones negativas, ya que no contribuye a reducir la dependencia de fuentes más contaminantes ni a promover una mayor sostenibilidad en la generación de electricidad.

<p align="center">
  
</p>

A pesar de estos esfuerzos, la persistente  escasez del derecho a la energía eléctrica en esta región se traduce en un aumento de los costos operativos tanto para empresas como para hogares (considerando la canasta familiar). Esta situación impacta negativamente en la disminución de  gastos . Según datos del INEI, entre el 60% y el 78.1% de la población total de Piura carece del paquete integrado de servicios, un indicador preocupante que subraya la necesidad urgente de abordar la brecha en el suministro eléctrico para mejorar la calidad de vida  fomentando el crecimiento económico en la región a lo largo del 2022.

<p align="center">
  
</p>

## **2. A Nivel Nacional**

<p align="justify">
El Perú ha demostrado un éxito notable en su historia reciente, experimentando un significativo aumento económico y disminución de la pobreza. Datos recientes hasta agosto de 2023 revelan un panorama más complejo, con la economía peruana enfrentando una contracción del PBI, desafíos en el mercado laboral y finanzas gubernamentales afectadas por la incertidumbre política y eventos climáticos, (Banco mundial, 2023).

Sin embargo, la reducción en -0.1% del PBI en el Perú durante noviembre del 2023 se debe al bajo nivel de consumo de bienes por parte de la población, lo cuál generó el descenso en la demanda interna en -2.0% debido al pequeño inversión bruta fija (-7.2%) respecto al reporte de la año anterior, (INEI, 2023).
</p>

<p align="center">
  
</p>

### **2.1. Sectores específicos**

<p align="justify">
En el tercer trimestre de 2023, se registró una disminución del 3.1% en la industria de comunicación y servicios informativos, indicando la presencia de posibles desafíos en este sector. En contraste, los sectores de Electricidad, gas y agua experimentaron un crecimiento del 3.0%, mientras que en transporte, almacenamiento, correo y mensajería se observó un crecimiento del 0.2% (INEI, 2023, pg. 9).

Estos datos indican dinámicas económicas divergentes en diferentes sectores, destacando la interconexión de la economía con la disponibilidad y estabilidad del suministro eléctrico. La disminución en el sector de telecomunicaciones podría sugerir una dependencia crítica de la energía para el funcionamiento de servicios clave en este sector.

El aumento en Electricidad, gas y agua resalta la importancia estratégica de estos servicios, subrayando la necesidad de un suministro eléctrico confiable para mantener la continuidad de actividades esenciales.

El ligero incremento en Transporte, almacenamiento, correo y mensajería puede indicar una conexión directa entre la movilidad y la energía, señalando cómo la privación de electricidad podría verse afectada indirectamente la eficiencia y crecimiento en estos sectores. En consecuencia, abordar esta problemática no solo beneficia directamente a la población, sino que también fortalece la infraestructura necesaria para el desarrollo económico en varios sectores clave del país.
</p>

<p align="center">
  
</p>

### **2.2. Producción Eléctrica**
<p align="justify">
Durante el tercer trimestre de 2023, se evidenció un incremento en el valor agregado bruto de la actividad de electricidad, gas y agua en Perú, destacando principalmente por el aumento en la producción de electricidad y gas (INEI, 2023). Este resultado positivo fue impulsado en gran medida por el notable aumento en la producción de energía eléctrica por parte de diversas empresas, incluyendo Enel Generación Perú y Engie Energía Perú (INEI, 2023), lo cual compensó las reducciones experimentadas por algunas otras empresas en el mismo sector.

Este crecimiento en la actividad de electricidad, gas y agua evidencia la capacidad del país para mantener y expandir sus sectores energéticos, contribuyendo al desarrollo económico y a la satisfacción de las demandas de diversos segmentos de la sociedad.
</p>

<p align="center">
  
</p>

## **3. A Nivel Mundial**

### **3.1. Contexto de la manufactura Eléctrica**
<p align="justify">
La hidroenergía emerge como el componente dominante, representando el 59% de la generación total (OLADE, 2020). Este enfoque en la hidroenergía destaca la dependencia de fuentes renovables, pero también plantea interrogantes sobre la diversificación y la resiliencia del sistema energético ante posibles variaciones climáticas.

La generación térmica no renovable, constituyendo el 39%, subraya el interés de evaluar los orígenes  de energía utilizadas (OLADE, 2020). La necesidad de transiciones hacia fuentes más limpias y sostenibles es evidente, especialmente dado el contexto global de cambio climático.

El estudio de la producción de energía eléctrica en la Zona Andina durante el periodo 2000-2019, se observa un cambio significativo en la matriz energética. En 2019, se generaron 259 TWh, marcando una disminución del 6.5% con respecto a 2018. Este cambio presenta oportunidades y desafíos que merecen atención.
La gráfica emitida por OLADE indica un cambio significativo en la matriz energética de la Zona Andina de 2000 a 2019. En 2019, se produjeron 259 TWh, reflejando una disminución del 6.5% a diferencia de otros años , según la información proporcionada.
</p>

<p align="center">
  
</p>

Dada la disminución en 2019, es esencial explorar estrategias para garantizar un suministro energético sostenible y resiliente en la Zona Andina. La inversión en la eficiencia energética son áreas clave a considerar y aprovechar las oportunidades emergentes en el panorama energético global.

### **3.2. Efecto económico según la  Estructura de Intensidad Energética**

El fenómeno del cambio estructural en la composición sectorial del Producto Interno Bruto (PIB) puede tener consecuencias significativas en la intensidad energética final en la Zona Andina, (OLADE, 2020). En este análisis, se destaca cómo una economía orientada hacia el sector de servicios puede influir en la optimización del uso de energía y, por lo tanto, en la intensidad energética final.

La transición hacia una economía con mayor enfoque en los servicios tiende a reducir la intensidad energética final. Este fenómeno queda representado en los diagramas Sankey que se presentan en los capítulos correspondientes a América Latina y el Caribe (ALC) y desglosados por país. Estos diagramas, basados en la Oferta Total (O.T.), incluyen Producción, Importación, Exportación, Variación de Inventario y No Aprovechado, (OLADE, 2020). Es esencial comprender cómo las dinámicas sectoriales influyen en la utilización de la energía y cómo estas fluctuaciones afectan la intensidad energética.

Es importante destacar que otras fuentes primarias, como el biogás, desechos vegetales, subproductos de la caña, madera, energía solar y eólica, varían según la disponibilidad de fuentes de energía en cada país. Este enfoque adaptativo destaca la importancia de evaluar y adaptar las estrategias energéticas a las características específicas de cada nación.

<p align="center">
  
</p>

<p align="center">
  
</p>

---
### Bibliografía

Compendio estadístico, Piura 2022. (n.d.). Informes Y Publicaciones - Instituto Nacional De Estadística E Informática - Plataforma Del Estado Peruano.<br>https://www.gob.pe/institucion/inei/informes-publicaciones/4133920-compendio-estadistico-piura-2022

Inei. (n.d.). Instituto Nacional de Estadística e Informática - Comportamiento de la Economía Peruana en el Tercer Trimestre de 2023.<br>https://discord.com/channels/1194096820691927152/1194096820691927157/1196944476908834888

Instituto Nacional de Estadística e Informática (2021) . “Acceso a los servicios básicos en el Perú 2021” . <br>https://www.inei.gob.pe/media/MenuRecursivo/publicaciones_digitales/Est/Lib1863/libro.pdf

Leandro Amaya (2023) . La luz que no llega: la pobreza energética también es un problema de género. LatFem.<br>https://latfem.org/la-luz-que-no-llega-la-pobreza-energetica-tambien-es-un-problema-de-genero/

Minem: Producción eléctrica nacional registró 4,445 GWh en febrero. (s. f.). Noticias - Ministerio de Energía y Minas - Plataforma del Estado Peruano.<br>https://www.gob.pe/institucion/minem/noticias/350449-minem-produccion-electrica-nacional-registro-4-445-gwh-en-febrero

Moran, M. (2017, November 22). Falta de acceso a la energía produce graves consecuencias en el desarrollo de los países menos adelantados. Desarrollo Sostenible.<br>https://www.un.org/sustainabledevelopment/es/2017/11/falta-de-acceso-la-energia-produce-graves-consecuencias-en-el-desarrollo-de-los-paises-menos-adelantados/ 

Organización latinoamericana de energía. (2023), Panorama energético de América latina y el carbe.<br>https://sielac.olade.org/WebForms/Reportes/VisorDocumentos.aspx?or=453&documentoId=10000017

Osinergmin, Encuesta Resistencia de consumo y usos de energía, (2019-2020).<br>https://cdn.www.gob.pe/uploads/document/file/2691020/ERCUE%20Electricidad%202019-2020.pdf

Perú Panorama general. (s. f.). World Bank.<br>https://www.bancomundial.org/es/country/peru/overview
