EdwinJaraOFC/VentusSolarisAnalyzer/docs/Documentacion/E03ContextoSocialEconomico.md

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

# Impactos Sociales de la Falta de Suministro Eléctrico en Piura, Perú

## 1. **A Nivel Regional**

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

<p align="center">
  
</p>


## 2. **A Nivel Nacional**

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

<p align="center">
  
</p>


## **3. A Nivel Mundial**

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

<div align="center"; style="display: flex; justify-content: space-between;">
  
  
</div>



# Impacto Económico de la Privación de Suministro a la Energía Eléctrica en Piura, Perú

## **1. A Nivel Regional**

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

<p align="center">
  
</p>


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

<p align="center">
  
</p>


## **2. A Nivel Nacional**

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

<p align="center">
  
</p>


### **2.1. Sectores específicos**

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

<p align="center">
  
</p>


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

<p align="center">
  
</p>


## **3. A Nivel Mundial**

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

<p align="center">
  
</p>


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

### **3.2. Efecto económico según la  Estructura de Intensidad Energética**

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

<p align="center">
  
</p>


<p align="center">
  
</p>


---
### Bibliografía

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

Perú Panorama general. (s. f.). World Bank.<br>https://www.bancomundial.org/es/country/peru/overview
