EdwinJaraOFC/VentusSolarisAnalyzer/Documentacion/Investigacion/I01DefiniciónDelProblema.md

<p align="left">
  
  <h1 align="center">Definición Del Problema</h1>
</p>

- **Problemática:** Falta de acceso a la electricidad en el colegio San José Obrero 15357 (Km.41 Carretera a Chulucanas). 
- **Ubicación de estudio:** San Jose Obrero (Colegio)
- **Departamento:** Piura
- **Provincia:** Morropón
- **Distrito:** Chulucanas

## Definición Formal del Problema
<h3 align="center">"La falta de electricidad en el colegio de San José Obrero impide el desarrollo educativo".</h1>

<p align="center">
  
</p>

## Características resaltadas de la zona
<p align="justify">
El plan de gestión de la Municipalidad Provincial de Morropón - Chulucanas para el periodo 2018 - 2022 hace referencia a aspectos significativos relacionados con el sitio en cuestión, tales como:
</p>

| <center>Características Resaltadas</center> | <center>Descripción</center> |
| --- | --- |
| <p align="center">**Aspectos Sociales**</p> | <p align="justify">La vulnerabilidad agrícola surge de la interacción de factores físicos, como los efectos climáticos en la productividad, y factores sociales, como el nivel educativo, el acceso a la tecnología y el capital disponible, entre otros. Además, se ha registrado un incremento en la tasa de deforestación debido al uso de la biomasa para la iluminación y la cocción (Morropón, M. D, 2017).</p> |
| <p align="center">**Clima**</p> | <p align="justify">El clima en la provincia de Morropón se caracteriza por ser cálido y seco, con una temperatura promedio de alrededor de 24-26°C. La evaporación es alta y las lluvias son irregulares, lo que puede generar ciclos de sequía y lluvias intensas.</p> |
| <p align="center">**Economía**</p> | <p align="justify">El área presenta una extensa cobertura vegetal con la presencia de árboles resistentes al clima, como plátanos, mangos, cítricos y otros. Además, se dedica a la ganadería, la cual representa la principal fuente de ingresos, al igual que la agricultura, destinada tanto al autoconsumo como a la comercialización.</p> |
| <p align="center">**Geografía**</p> | <p align="justify">La región presenta una variedad de pisos ecológicos y diversidad de suelos, así como una amplia gama de estratos socioeconómicos y actividades económicas predominantes.</p> |

<p align="center">
  
</p>

## Herramientas para identificar el problema
### Mapa de Empatía
<p align="center">
  
</p>

### Mapa del viaje del cliente
<p align="center">
  
</p>

### Diagrama Causa-Efecto
<p align="center">
  
</p>

## Acciones Propuestas
| <center>Acciones Propuestas</center> | <center>Descripción</center> |
| --- | --- |
| <p align="center">**Catalizador para Desarrollo Sostenible**</p> | <p align="justify">Más allá de resolver la carencia de energía, se busca establecer un cimiento sólido para el desarrollo sostenible y equitativo.</p> |
| <p align="center">**Generadores para controlar la velocidad del viento**</p> | <p align="justify">Estos generadores podrían utilizarse para alimentar sistemas de almacenamiento de energía, como baterías, que permitan aprovechar la energía generada durante vientos fuertes para su uso posterior.</p> |
| <p align="center">**Implementación de energía híbrida**</p> | <p align="justify">La iniciativa clave consiste en la instalación de un sistema de energía híbrida, considerando tanto fuentes eólicas como solares.</p> |
| <p align="center">**Sistemas fotovoltaicos**</p> | <p align="justify">La integración de sistemas fotovoltaicos complementará la generación de energía híbrida, aprovechando la radiación solar disponible en la región.</p> |

## Propuesta Formal de Solución
<h3 align="center">
"Crear un sistema de baja potencia a base de sensores que puedan monitorear las características de la radiación solar y la velocidad del viento, con el objetivo de transmitir datos desde los sensores y dispositivos IoT que enviarán los datos recopilados a una plataforma en la nube de gestión centralizada".
</h3>

---
### Bibliografía
Defensoría del Pueblo (2021a). Defensoría del Pueblo reitera la urgencia de garantizar acceso a la educación en zonas rurales de Piura.<br>https://www.defensoria.gob.pe/defensoria-del-pueblo-reitera-la-urgencia-de-garantizar-acceso-a-la-educacion-en-zonas-rurales-de-piura/

Defensoría del Pueblo (2021b). Defensoría del Pueblo reitera la urgencia de garantizar acceso a la educación en zonas rurales de Piura.<br>https://www.defensoria.gob.pe/wp-content/uploads/2021/10/NP-1359-2021.pdf

Morropón, M. D. (2017). Plan de desarrollo económico de la provincia de Morropón 2018-2022.<br>http://www.cipca.pe/wp-content/uploads/2022/06/PLANDE-MORROPON.pdf 

Pazmiño Echeverría, J. (2007). Proyecto de inversión para el suministro de electricidad en la comunidad facundo vela-provincia de bolìvar, mediante soluciones individuales de equipos fotovoltaicos (Tesis de Grado).<br>https://www.dspace.espol.edu.ec/handle/123456789/6892
