EdwinJaraOFC/VentusSolarisAnalyzer/Prototipo/Hardware/H04Planos/MALETIN_COMPLETO.pdf

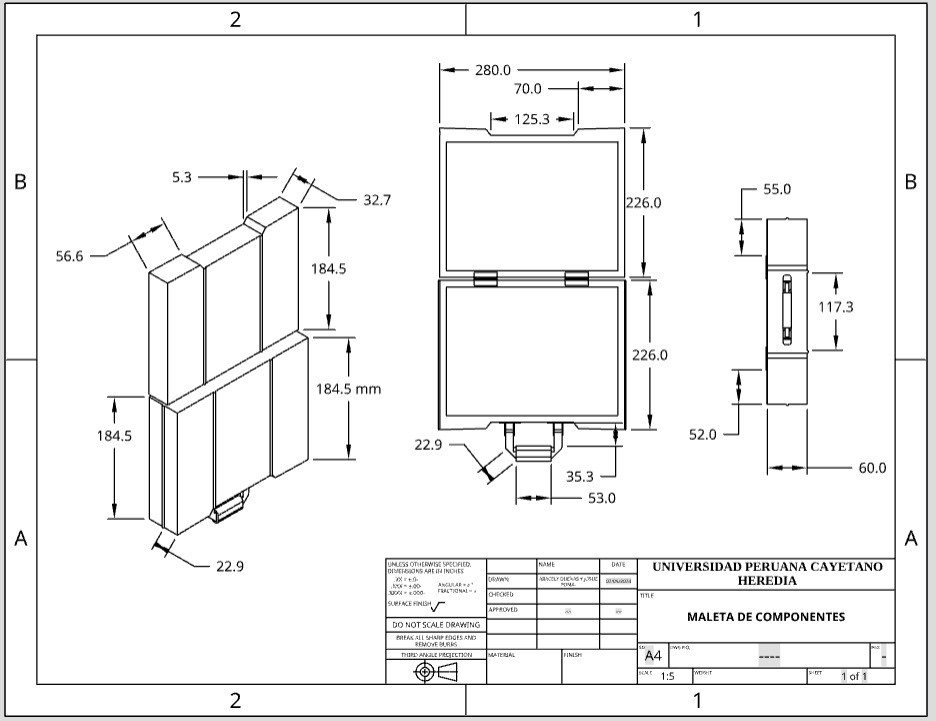
[picture p63: page 1]
