EdwinJaraOFC/VentusSolarisAnalyzer/Prototipo/Software/DiagramaDeFlujo.pdf

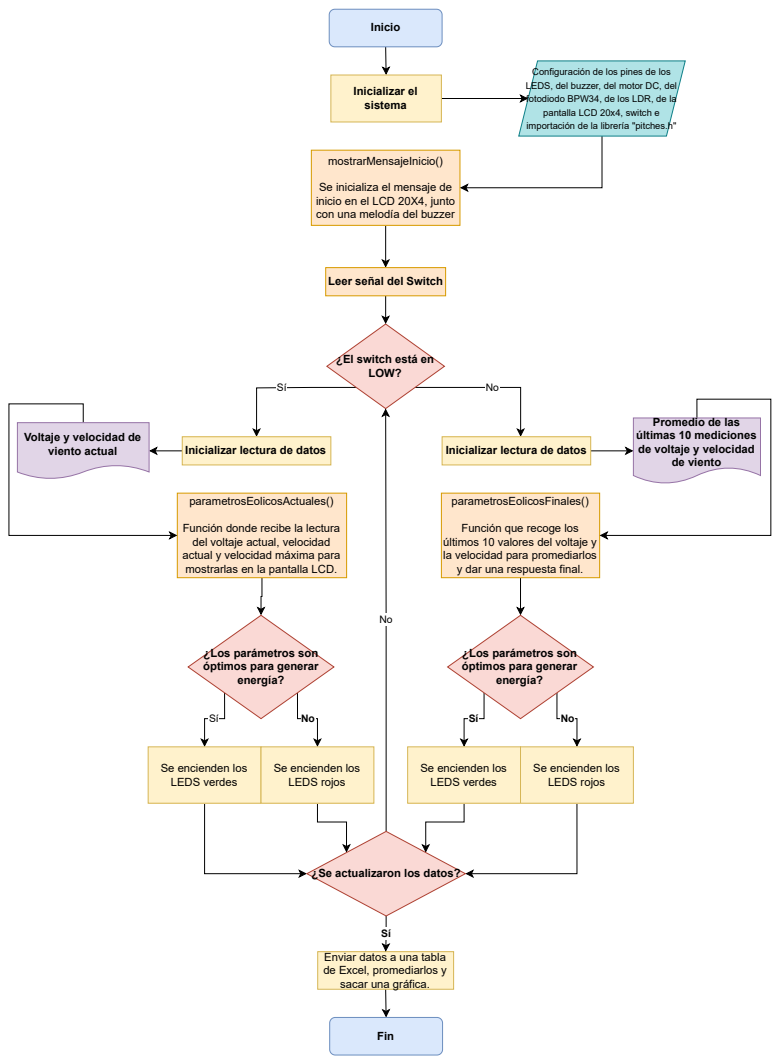
[picture p74: page 1]
Inicio; mostrarMensajeInicio(); parametrosEolicosActuales(); parametrosEolicosFinales(); Inicializar el sistema; Fin

Configuración de los pines de los
LEDS, del buzzer, del motor DC, del
fotodiodo BPW34, de los LDR, de la
pantalla LCD 20x4, switch e
importación de la librería "pitches.h"

Se inicializa el mensaje de
inicio en el LCD 20X4, junto
con una melodía del buzzer

Leer señal del Switch

¿El switch está en
LOW?

Promedio de las
últimas 10 mediciones
de voltaje y velocidad
de viento

Voltaje y velocidad de
viento actual

Inicializar lectura de datos

Función donde recibe la lectura
del voltaje actual, velocidad
actual y velocidad máxima para
mostrarlas en la pantalla LCD.

Función que recoge los
últimos 10 valores del voltaje y
la velocidad para promediarlos
y dar una respuesta final.

¿Los parámetros son
óptimos para generar
energía?

Se encienden los
LEDS verdes

LEDS rojos

¿Se actualizaron los datos?

Enviar datos a una tabla
de Excel, promediarlos y
sacar una gráfica.
